emmismyname/-smart-car/smart-elecar/USER/src/carcontrol.c

#include "carcontrol.h"
int err_speed = 0;
int running_mode = 1;		// 1是待机motor等于0 2是停车 3普通寻迹（计时器）
uint8 trace_flag = 0;		// 寻迹开关
int current_number = 0; // 扫描开始标志位
int trigflag_beep = 1;	// 蜂鸣器防误触
int outward_basin = 0;	// 出库标志位
uint8 avoid_move = 0;		// 避障开关
uint8 TOF_object = 0;		// 未检测到 1检测到障碍物 2检测障碍物后开始处理 3避障结束
int TOF_barrier[9] = {0};
int OUTP_flag = 0;		// 定时器启动计算 0不启用运动控制 1右出库 2左出库 3上坡直行
uint8 start_flag = 0; // 发车标志位
uint8 stop_flag = 0;	// 停车标志位
uint8 small_radiu = 0;

// 避障
float err_angle_rate = 0;
extern int outtoin_flag = 0;
float yaw_target = 0;		 // 避障角度
float out_distance = 18; // 避障距离
float in_distance = 14;	 // 回正距离
float out_angle = 65;		 // 避障目标角度
float in_angle = -35;		 // 回正目标角度

//  库状态
int pack_mode = 0;
int strategy_mode = 0;

// 入库
float intop_angle = 80;		// 入库目标角度
float intop_distance = 15; // 入库距离
float intop_radiu = 0;		// 入库圆环
/***************************************************************************************/

// 出库
float outp_angle = 70;		 // 出库目标角度
float outp_distance = 13; // 入库距离
float outp_radiu = -22;		 // 入库圆环
/****************************************************************************************/


/**************************************江心一号************************************/
//发车
int16 route_distance=0;//定航距离




/****************************************************************************************/


//-------------------------------------------------------------------------------------------------------------------
//  @brief      运动模式切换
//  @param
//  @param
//  @return
//-------------------------------------------------------------------------------------------------------------------
void mode_choose(int move_mode) // 运动模式切换
{
	// int temp_counter=1;
	if (trace_flag == 0) // 完全停车
	{
		// 当霍尔检测到时候操作trace_flag==0停止寻迹
		Target_speed = 0;
		Target_Speed_L = 0;
		Target_Speed_R = 0;
		motor_flag = 0;
	}
	else if (trace_flag == 1)
	{
		switch (move_mode)
		{
		case 1: // 待机
		{
		}
		break;
		case 2: // 停止pid
		{
			Target_Speed_L = 0;
			Target_Speed_R = 0;
		}
		break;
		case 3: // 直行pid
		{
			motor_flag = 1; // 电机输出
			Target_Speed_L = Target_speed - PID_Loc_Control(&Forward_PID, Forward_PID.err) - z_gyro * gyro_d;
			Target_Speed_R = Target_speed + PID_Loc_Control(&Forward_PID, Forward_PID.err) + z_gyro * gyro_d;
		}
		break;
		case 4: // 弯道输出
		{
			motor_flag = 1; // 电机输出
			Target_Speed_L = Target_speed - PID_Loc_Control(&Forward_PID, Forward_PID.err) - PID_Loc_Control(&Swerve_PID, err) - z_gyro * gyro_d;
			Target_Speed_R = Target_speed + PID_Loc_Control(&Forward_PID, Forward_PID.err) + PID_Loc_Control(&Swerve_PID, err) + z_gyro * gyro_d;
		}
		break;
		case 8: // 角度环调参
		{
			motor_flag = 1; // 电机输出
			Target_Speed_L = Target_speed - PID_Loc_angle_rate_Control(&Pout_rate_PID, err_angle_rate);
			Target_Speed_R = Target_speed + PID_Loc_angle_rate_Control(&Pout_rate_PID, err_angle_rate);
		}
		break;
		default:
			break;
		}
	}
}

void strategy_choose(int mode)
{
	switch (mode)
	{
	case 0:
		in_angle = 0;
		in_distance = 0;
		out_angle = 0;
		out_distance = 0;
		break;
	case 1: // 避障
		in_angle = -60;
		in_distance = 50;
		out_angle = 30;
		out_distance = 70;
		break;
	case 2: // 右出右后
		in_angle = -60;
		in_distance = 50;
		out_angle = 30;
		out_distance = 70;
		break;

	default:
		break;
	}
} // void obstacle_avoidance(float out_distance,float in_distance,float out_angle,float in_angle) //避障处理

void work(int mode)
{
	switch (mode)
	{
	case 0:
	  base_speed=220;
		pretoreadyL_round_distance = 11;
		pretoreadyR_round_distance = 20;
		leftround_diff = 15;
		rigtround_diff = 20;
		leftround_ready = 130;
		rigtround_ready = 140;
		leftround_yawtarget = 65;
		rigtround_yawtarget = -65;
		lmid_del = -20;
		rmid_del = -15;
		break;

	default:
		break;
	}
}

//{

//}
int obstacle_avoidance(float out_angle1, float in_angle1, float target_out_distance1, float target_in_distance1) // 避障处理
{
	int res = 1;
	if (distance_L + distance_R < 2000 * target_out_distance1)
	{
		running_mode = 8;
		Target_speed = base_speed - 20;
		motor_flag = 1; // 电机输出
		yaw_target = out_angle1;
		mode_choose(running_mode);
	}
	else if (distance_L + distance_R > 2000 * target_out_distance1)
	{
		outtoin_flag = 1;
	}
	if (outtoin_flag == 1 && distance_L + distance_R < 2000 * (target_out_distance1 + target_in_distance1))
	{
		running_mode = 8;
		Target_speed = base_speed - 20;
		motor_flag = 1; // 电机输出
		yaw_target = in_angle1;
		mode_choose(running_mode);
	}
	else if (distance_L + distance_R > 2000 * (target_out_distance1 + target_in_distance1))
	{
		res = 0;
		TOF_object = 0; // 关闭
		outtoin_flag = 0;
	}

	return res;
}
