emmismyname/-smart-car/USER/src/DMP.c

/*****************************************************
功能:	采集MPU6050 DMP 数据
CPU:	STC89C54RD+
晶震:	11.0592
环境:	Keli2.0
语言: 	c
作者：	XW1005
来源：	移植 Jeff Jrowberg 公开的程序。
目的：
sda 或则scl 为高时是:释放总线
*****************************************************/
#include "DMP.h"

float Q[4];			  // 四元数
uint8_t dmpdatas[42]; // DMP数据

// 以下的 firmware 及 config update 数据来自于 Jeff Jrowberg 公开的程序
/* ================================================================================================ *
| Default MotionApps v2.0 42-byte FIFO packet structure:                                           |
|                                                                                                  |
| [QUAT W][      ][QUAT X][      ][QUAT Y][      ][QUAT Z][      ][GYRO X][      ][GYRO Y][      ] |
|   0   1   2   3   4   5   6   7   8   9  10  11  12  13  14  15  16  17  18  19  20  21  22  23  |
|                                                                                                  |
| [GYRO Z][      ][ACC X ][      ][ACC Y ][      ][ACC Z ][      ][      ]                         |
|  24  25  26  27  28  29  30  31  32  33  34  35  36  37  38  39  40  41                          |
* ================================================================================================ */
uint8_t code dmpmemorydata[1929] =
	{
		// bank 0, 256 bytes
		0xFB, 0x00, 0x00, 0x3E, 0x00, 0x0B, 0x00, 0x36, 0x00, 0x01, 0x00, 0x02, 0x00, 0x03, 0x00, 0x00,
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
		0x07, 0x7E, 0x01, 0x30,
		0x07, 0x46, 0x01, 0x9A,
		0x07, 0x47, 0x04, 0xF1, 0x28, 0x30, 0x38,
		0x07, 0x6C, 0x04, 0xF1, 0x28, 0x30, 0x38,
		0x02, 0x16, 0x02, 0x00, 0x01,
		/* 上行最后一个数据调整FIFO rate :0x01=100HZ,0x02=66HZ,0x03=50HZ ,0x04=40HZ,0x05=33.33HZ,
		// 可从 datasheet 公式推算
		//dmp updates
		0x01,   0xB2,   0x02,   0xFF, 0xFF,
		0x01,   0x90,   0x04,   0x09, 0x23, 0xA1, 0x35,
		0x01,   0x6A,   0x02,   0x06, 0x00,
		0x01,   0x60,   0x08,   0x00, 0x00, 0x00, 0x00, 0x00, 0x00, 0x00, 0x00,
		0x00,   0x60,   0x04,   0x40, 0x00, 0x00, 0x00,
		0x01,   0x62,   0x02,   0x00, 0x00,
		0x00,   0x60,   0x04,   0x00, 0x40, 0x00, 0x00*/
};

uint8_t code dmpUpdates[47] =
	{
		0x01, 0xB2, 0x02, 0xFF, 0xFF,
		0x01, 0x90, 0x04, 0x09, 0x23, 0xA1, 0x35,
		0x01, 0x6A, 0x02, 0x06, 0x00,
		0x01, 0x60, 0x08, 0x00, 0x00, 0x00, 0x00, 0x00, 0x00, 0x00, 0x00,
		0x00, 0x60, 0x04, 0x40, 0x00, 0x00, 0x00,
		0x01, 0x62, 0x02, 0x00, 0x00,
		0x00, 0x60, 0x04, 0x00, 0x40, 0x00, 0x00

};

/*
加载 DMP代码到
返回值  (1=成功,0=失败)
*/
uint8_t loadfirmware(void)
{
	uint16_t datanum = 0; // DMP固件写入标志位
	uint8_t ye, i /*, j*/;
	uint8_t bank = 0; // 段（256个数据一段）
	uint8_t addr = 0;

	for (; bank < 8; bank++)
	{
		if (bank == 7) // 这里的作用就是区分最后一段数据
			i = 8;
		else
			i = 16;
		for (ye = 0; ye < i; ye++)
		{
			MPU_Write_Byte(0x6d, bank);
			MPU_Write_Byte(0x6e, addr);
			MPU_Write_Len(0x6f, 16, dmpmemorydata + datanum);
			datanum += 16;
			addr += 16;
		}
	}
	MPU_Write_Byte(0x6d, 7);
	MPU_Write_Byte(0x6e, addr);
	MPU_Write_Len(0x6f, 9, dmpmemorydata + datanum);
	datanum += 9;
	return 1;
}

uint8_t loadcfgupd(void) // DMP设置
{
	uint8_t line;			// 一共需要写入30条设置数据
	uint8_t bank;			// 页
	uint8_t datacounts = 0; // DMP设置数据标志位
	uint8_t bytes2write;	// 数据长度。
	uint8_t offset;			// 偏移地址
	uint8_t writingcounts;	// 数据写入标志与bytes2write一同使用
	uint8_t special;

	for (line = 0; line < 30; line++)
	{
		bank = dmpcfgupddata[datacounts++];
		offset = dmpcfgupddata[datacounts++];
		bytes2write = dmpcfgupddata[datacounts++];
		MPU_Write_Byte(0x6d, bank);
		MPU_Write_Byte(0x6e, offset);
		MPU_Write_Len(0x6f, bytes2write, dmpcfgupddata + datacounts);
		writingcounts = bytes2write;
		datacounts += bytes2write;
		if (0 == bytes2write)
		{
			special = dmpcfgupddata[datacounts++];
			if (0x01 == special)
			{
				// 设置零运动中断启用（真）;
				// 设置FIFO缓冲区溢出启用（真）;
				// 设置DMP启用（真）;
				MPU_Write_Byte(MPU_INT_EN_REG, 0x32);
			}
			else
				return 0;
		}
	}
	return 1;
}

/*最后更新DMP*/
uint8_t xdmpUpdates(uint8_t datacounts)
{
	uint8_t writingcounts, bank, offset, bytes2write;
	bank = dmpUpdates[datacounts++];
	offset = dmpUpdates[datacounts++];
	bytes2write = dmpUpdates[datacounts++];
	MPU_Write_Byte(0x6d, bank);
	MPU_Write_Byte(0x6e, offset);
	MPU_Write_Len(0x6f, bytes2write, dmpUpdates + datacounts);
	writingcounts = bytes2write;
	datacounts += bytes2write;
	return 1;
}

/*读取 FIFO 计数*/
uint16_t getFIFOCount()
{
	uint8_t i[2];
	MPU_Read_Len(MPU_FIFO_CNTH_REG, 2, i);
	return ((i[0] << 8) + i[1]);
}

/*FIFO数据读取
参数 *Data	存储数据的地址
返回值 (1=读取成功,0读取失败)
*/
uint8_t readdmp(uint8_t *Data)
{
	return !MPU_Read_Len(MPU_FIFO_RW_REG, 42, Data);
}

// 加载并配置 DMP 数字运动处理引擎
uint8_t dmpInitialize(void)
{
	uint8_t hwRevision, otpValid, mpuIntStatus /*fifoBuffer[128]*/;
	uint8_t xgOffsetTC, ygOffsetTC, zgOffsetTC;
	uint16_t fifoCount;
	MPU_Write_Bit(MPU_PWR_MGMT1_REG, 7, 1); // 复位 MPU6050
	MPU_Delay_Ms(30);
	MPU_Write_Bit(MPU_PWR_MGMT1_REG, 6, 0); // 禁止睡眠模式
	MPU_Write_Byte(0x6D, 0x70);				// 写入一个字节数据到0x6d寄存器(选择用户 bank)
	MPU_Write_Byte(0x6E, 0x06);				// 写入一个字节数据到0x6e寄存器(选择存储字节)
	MPU_Read_Len(0x6F, 1, &hwRevision);		// 读取
	MPU_Write_Byte(0x6D, 0);				// 重置内存 bank 选择
	MPU_Read_Bit(0x00, 0, &otpValid);		// 读取 OTP bank 有效标志
	MPU_Read_Bits(0x00, 6, 6, &xgOffsetTC); // 读陀螺偏置TC值 X
	MPU_Read_Bits(0x01, 6, 6, &ygOffsetTC); // 读陀螺偏置TC值 Y)
	MPU_Read_Bits(0x02, 6, 6, &zgOffsetTC); // 读陀螺偏置TC值 Z
	// MPU_Write_Byte(MPU_I2CSLV0_ADDR_REG,0x7f);	//设置从0地址 0x7
	// MPU_Write_Bit(MPU_USER_CTRL_REG,5,0);	//禁用I2C主模式
	// MPU_Write_Byte(MPU_I2CSLV0_ADDR_REG,0x68);	//这里可能要改。还没有弄明白这里
	MPU_Write_Bit(MPU_USER_CTRL_REG, 1, 1); // I2C总线主控复位
	MPU_Delay_Ms(20);
	if ((loadfirmware()) == 0)
		return 0; // 加载
	if ((loadcfgupd()) == 0)
		return 0;								   // 配置DMP
	MPU_Write_Bits(MPU_PWR_MGMT1_REG, 2, 3, 0x03); // 设置时钟脉冲源Z陀螺
	MPU_Write_Byte(MPU_INT_EN_REG, 0x12);		   // 设置DMP和FIFO_OFLOW启用中断
	MPU_Write_Byte(MPU_SAMPLE_RATE_REG, 4);		   // 设置采样率为200 hz  (1khz / (1 + 4) = 200 Hz)
	MPU_Write_Bits(MPU_CFG_REG, 5, 3, 0x1);		   // 设置外部帧同步TEMP_OUT_L[0]
	MPU_Write_Bits(MPU_CFG_REG, 2, 3, 0x03);	   // 设置DLPF带宽42赫兹
	MPU_Write_Bits(MPU_GYRO_CFG_REG, 4, 2, 0x03);  // 陀螺灵敏度设置为+ / - 2000 deg/sec
	MPU_Write_Byte(0x70, 0x03);					   // 设置DMP配置字节（功能未知）
	MPU_Write_Byte(0x71, 0x00);					   // 设置DMP配置字节（功能未知）
	MPU_Write_Bit(0x00, 0, 0);					   // 清除OTP Bank 标志
	MPU_Write_Bits(0x00, 6, 6, 0);				   // 设置X 陀螺抵消TCs之前的值
	MPU_Write_Bits(0x01, 6, 6, 0);				   // 设置Y 陀螺抵消TCs之前的值
	MPU_Write_Bits(0x02, 6, 6, 0);				   // 设置Z 陀螺抵消TCs之前的值
	if (xdmpUpdates(0) == 0)
		return 0; // 最后更新1/7(函数未知)dmpUpdates数组第一行
	if (xdmpUpdates(5) == 0)
		return 0;							// 最后更新2/7(函数未知)dmpUpdates数组第二行
	MPU_Write_Bit(MPU_USER_CTRL_REG, 2, 1); // 复位 FIFO
	fifoCount = getFIFOCount();				// 读取 FIFO 计数
								// readdmp(fifoCount,fifoBuffer);	//读取FIFO里的数据
	MPU_Write_Bit(MPU_USER_CTRL_REG, 2, 1); // 复位 FIFO

	MPU_Write_Byte(MPU_MOTION_DET_REG, 2);	// 运动检测阈值设置为2
	MPU_Write_Byte(0x21, 156);				// 零运动检测阈值为156
	MPU_Write_Byte(0x20, 80);				// 设置运动检测持续时间至80
	MPU_Write_Byte(0x22, 0);				// 设置零运动检测时间0
	MPU_Write_Bit(MPU_USER_CTRL_REG, 2, 1); // 复 位 FIFO
	MPU_Write_Bit(MPU_USER_CTRL_REG, 6, 1); // 使能 FIFO
	MPU_Write_Bit(MPU_USER_CTRL_REG, 7, 1); // 使能 DMP
	MPU_Write_Bit(MPU_USER_CTRL_REG, 3, 1); // 复位 DMP
	if (xdmpUpdates(12) == 0)
		return 0; // 最后更新3/7(函数未知)dmpUpdates数组第三行
	if (xdmpUpdates(17) == 0)
		return 0; // 最后更新4/7(函数未知)dmpUpdates数组第四行
	if (xdmpUpdates(28) == 0)
		return 0; // 最后更新5/7(函数未知)dmpUpdates数组第五行
	while ((fifoCount = getFIFOCount()) < 3)
		;									// 等待 FIFO 计数 > 2
	MPU_Write_Bit(MPU_USER_CTRL_REG, 2, 1); // 复位 FIFO
	// readdmp(fifoCount,fifoBuffer);	//读取FIFO里的数据
	MPU_Read_Len(MPU_INT_STA_REG, 1, &mpuIntStatus); // 读取中断状态
	if (xdmpUpdates(35) == 0)
		return 0; // 最后更新6/7(函数未知)dmpUpdates数组第六行
	while ((fifoCount = getFIFOCount()) < 3)
		;									// 等待 FIFO 计数 > 2
	MPU_Write_Bit(MPU_USER_CTRL_REG, 2, 1); // 复位 FIFO
	// readdmp(fifoCount,fifoBuffer);	//读取FIFO里的数据
	MPU_Read_Len(MPU_INT_STA_REG, 1, &mpuIntStatus); // 读取中断状态
	if (xdmpUpdates(40) == 0)
		return 0;							// 最后更新7/7(函数未知)dmpUpdates数组第七行
	MPU_Write_Bit(MPU_USER_CTRL_REG, 7, 0); // 禁用DMP(稍后您打开它)
	MPU_Write_Bit(MPU_USER_CTRL_REG, 2, 1); // 复位 FIFO
	MPU_Read_Len(MPU_INT_STA_REG, 1, &mpuIntStatus);
	// 星期六 (2014/06/28)
	return 1;
}

/*初始化MPU6050*/
void initMPU6050(void)
{
	MPU_Write_Bits(MPU_PWR_MGMT1_REG, 2, 3, 0x01); // 电源管理
	MPU_Write_Bits(MPU_GYRO_CFG_REG, 4, 2, 0x00);  // 设置陀螺仪量程 250/s
	MPU_Write_Bits(MPU_ACCEL_CFG_REG, 4, 2, 0x00); // 设置加速度量程 2G
	MPU_Write_Bit(MPU_PWR_MGMT1_REG, 6, 1);		   // 电源管理MUP进入睡眠模式
}

/*验证MPU6050连接*/
uint8_t getDeviceID(void)
{
	uint8_t b = 0;								// 临时变量
	MPU_Read_Bits(MPU_DEVICE_ID_REG, 6, 6, &b); // 读取i2c固定地址，去掉最高位和最低位这两位数据
	return b == 0x34;							// 判断B是否等于0x34，如果等于返回1，不等于返回0(库的是0x38)
}

void MPU6050_DMP_Init(void)
{
	initMPU6050();				   // 初始化
	if (getDeviceID())			   // 验证连接是否正常(读取MPU6050的I2C地址)
		while (!(dmpInitialize())) // 加载并配置运动库
		{
			printf("Initializing");
		}
	MPU_Write_Bit(MPU_USER_CTRL_REG, 2, 1); // 复位 FIFO
	MPU_Write_Bit(MPU_USER_CTRL_REG, 7, 1); // 使能DMP
}

void MPU6050_Refresh_DMP(void)
{
	static uint8_t zd;
	static uint16_t i;
	i = getFIFOCount();					   // 读取FIFO计数
	MPU_Read_Len(MPU_INT_STA_REG, 1, &zd); // 读取中断状态
	if ((zd & 0x10) || i >= 840)		   // 判断FIFO是否溢出
	{
		MPU_Write_Bit(MPU_USER_CTRL_REG, 2, 1); // 复位 FIFO
	}
	else if (zd & 0x02)
	{
		while (i < 42)
			i = getFIFOCount();
		if (readdmp(dmpdatas)) // 读取FIFO数据
		{
			Q[0] = ((int16_t)dmpdatas[0] << 8 | dmpdatas[1]) / 16384.;
			Q[1] = ((int16_t)dmpdatas[4] << 8 | dmpdatas[5]) / 16384.;
			Q[2] = ((int16_t)dmpdatas[8] << 8 | dmpdatas[9]) / 16384.;
			Q[3] = ((int16_t)dmpdatas[12] << 8 | dmpdatas[13]) / 16384.;
		}
	}
}
