emmismyname/-smart-car/USER/inc/mycode.h

#ifndef __MYCODE_H_
#define __MYCODE_H_



#include "MPU6050.h"
#include "DMP.h"
#include "motor.h"
#include "data.h"
#include "assistant.h"
#include "car_state.h"
#include "carcontrol.h"


extern float get_error1;


#endif
