emmismyname/-smart-car/smart-elecar/USER/inc/MyCode.h

#ifndef __MYCODE_H_
#define __MYCODE_H_

#include "motor.h"
#include "adc_aquire.h"
#include "imu.h"
#include "eeprom.h"
#include "carcontrol.h"
#include "MPU6050.h"
#include "DMP.h"
#include "uart_read.h"
#include "uart_send.h"
#include "car_state.h"

#endif
