emmismyname/-smart-car/smart-elecar/USER/src/keyboard.c

#include "keyboard.h"

uint8 sw1_status;
uint8 sw2_status;

// 开关状态变量
uint8 key1_status = 1;
uint8 key2_status = 1;
uint8 key3_status = 1;
uint8 key4_status = 1;

// 上一次开关状态变量
uint8 key1_last_status;
uint8 key2_last_status;
uint8 key3_last_status;
uint8 key4_last_status;

// 开关标志位
uint8 key1_flag;
uint8 key2_flag;
uint8 key3_flag;
uint8 key4_flag;

int button_switch = 1; // 第三和第四个按键的开关，调参开关开关与否
